shaunirwin/self_balancing_robot/electronics/cable_harnesses/cable_harness_powerbank_to_esp32.yml

connectors:
  X1:
    type: USB A      # connector type J. Connects to powerbank to cable
    subtype: male
    pinlabels: [GND, 5V]       # ENCODER_VCC: 3.3V-24V
  X2:
    type: USB C    # connector type I. Connects cable to the ESP32 board for power
    subtype: male
    pinlabels: [GND, 5V]

cables:
  W1:       # cable harness 2
    gauge: 0.25 mm2
    length: 0.2
    color: BK  # Cable jacket color
    color_code: DIN
    wirecount: 2
    shield: true

connections:
  -
    - X1: [1,2]
    - W1: [1,2]
    - X2: [1,2]
  -
    #- Key: GND
    - X1: 1
    - W1: s
