shaunirwin/self_balancing_robot/firmware/platformio_projects/self_balancing_robot/src/secrets_template.h

#pragma once

// Copy this template to secrets.h, then enter your Wi-Fi credentials there.
// Do not commit secrets.h.
const char* ssid = "REPLACE_WITH_YOUR_SSID";
const char* password = "REPLACE_WITH_YOUR_PASSWORD";
