shaunirwin/self_balancing_robot/software/webserver/server.py

from http.server import SimpleHTTPRequestHandler, HTTPServer
import json

class CORSRequestHandler(SimpleHTTPRequestHandler):
    def end_headers(self):
        self.send_header('Access-Control-Allow-Origin', '*')
        self.send_header('Access-Control-Allow-Methods', 'GET, POST, OPTIONS')
        self.send_header('Access-Control-Allow-Headers', 'Content-Type')
        SimpleHTTPRequestHandler.end_headers(self)

    def do_OPTIONS(self):
        self.send_response(200, "ok")
        self.end_headers()

    def do_POST(self):
        if self.path == '/your-endpoint':
            content_length = int(self.headers['Content-Length'])
            post_data = self.rfile.read(content_length)
            data = json.loads(post_data)
            print(f"Received data: {data}")

            response = {
                'status': 'success',
                'received_data': data
            }
            self.send_response(200)
            self.send_header('Content-Type', 'application/json')
            self.end_headers()
            self.wfile.write(json.dumps(response).encode())

if __name__ == "__main__":
    server_address = ('', 8000)
    httpd = HTTPServer(server_address, CORSRequestHandler)
    print("Serving on port 8000...")
    httpd.serve_forever()
